matejpokorny/40-percent-ortholinear-rpi-pico-keyboard/firmware/pins.py

import board

row_pins = (
    board.GP0,  # Row 1
    board.GP1,  # Row 2
    board.GP2,  # Row 3
    board.GP3,  # Row 4
)

col_pins = (
    board.GP4,  # Col 1
    board.GP5,  # Col 2
    board.GP6,  # Col 3
    board.GP7,  # Col 4
    board.GP8,  # Col 5
    board.GP9,  # Col 6
    board.GP10,  # Col 7
    board.GP11,  # Col 8
    board.GP12,  # Col 9
    board.GP13,  # Col 10
)
